cs2dsb/zcssr/firmware/src/board/mod.rs

/*
    MCU is STM32F103RCTx
    256K Flash
    48K SRAM
*/

mod constants;
pub use constants::*;

mod aliases;
pub use aliases::*;

mod output;
pub use output::*;

mod multi_pwm;
pub use multi_pwm::*;

mod pulse_ssr;
pub use pulse_ssr::*;

mod clear_interrupt;
pub use clear_interrupt::*;

mod itm;
pub use itm::*;

mod configure;
pub use configure::*;
